Gnoth-404/Movement-Detection-using-24Ghz-Radar/hardware/10_SubCircuit_4thPassFilter/20_Simulation/sdhd_lab.asc

C1: cap; 100n
C2: polcap; 4.7µ
C3: cap; 1.5n
C4: polcap; 22µ
C5: polcap; 4.7µ
C6: cap; 3.3n
R1: res; 1k
R2: res; 1k
R3: res; 2.2k
R4: res; 33k
R5: res; 220k
R6: res; 100k
R7: res; 100
U1: UniversalOpAmp
U2: UniversalOpAmp
V1: voltage; 5
V2: voltage; ""; AC 1
Named nets: 0, out, in
.ac oct 10000 1 100000
* Gain Analysis Command
.meas gain_max MAX V(out)/V(in) FROM 1Hz TO 1Meg
 
* Corner Frequency Analysis Commands
.measure AC f_lower WHEN V(out)={Gain_max/sqrt(2)}
.measure f_upper when V(out)/V(in) = gain_max/sqrt(2) from 1MHz
 
* Low Pass Frequency Analysis Command
.measure f_low when V(out)/V(in) = gain_max/sqrt(2) from 1Hz
 
* High Pass Frequency Analysis Command
.measure f_high when V(out)/V(in) = gain_max/sqrt(2) from 1MHz
.lib opamp.sub
