Gnoth-404/Movement-Detection-using-24Ghz-Radar/software/firmware/Matlab_FFT.cydsn/bsw/led.c

/**
* \file <filename>
* \author <author-name>
* \date <date>
*
* \brief <Symbolic File name>
*
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
* \warning This software is a PROTOTYPE version and is not designed or intended for use in production, especially not for safety-critical applications!
* The user represents and warrants that it will NOT use or redistribute the Software for such purposes.
* This prototype is for research purposes only. This software is provided "AS IS," without a warranty of any kind.
*/

/*****************************************************************************/
/* Include files                                                             */
/*****************************************************************************/

#include "project.h"
#include "led.h"


/*****************************************************************************/
/* Local pre-processor symbols/macros ('#define')                            */
/*****************************************************************************/

/*****************************************************************************/
/* Global variable definitions (declared in header file with 'extern')       */
/*****************************************************************************/

/*****************************************************************************/
/* Local type definitions ('typedef')                                        */
/*****************************************************************************/



/*****************************************************************************/
/* Local variable definitions ('static')                                     */
/*****************************************************************************/


static LED_ONOFF_t LED__state[LED_ALL] = {LED_OFF, LED_OFF, LED_OFF}; /**< On/Off State of the LED, TRUE is on */

const static uint16 LED__Pulse_Width[256] = {
    0, 1, 1, 1, 1, 1, 1, 1, 1, 2, 2, 2, 2, 2, 2, 2, 2, 2, 2, 2, 2, 3,
    3, 3, 3, 3, 3, 3, 4, 4, 4, 4, 4, 4, 5, 5, 5, 5, 5, 6, 6, 6, 6, 7,
    7, 7, 8, 8, 8, 9, 9, 10, 10, 10, 11, 11, 12, 12, 13, 13, 14, 15,
    15, 16, 17, 17, 18, 19, 20, 21, 22, 23, 24, 25, 26, 27, 28, 29,
    31, 32, 33, 35, 36, 38, 40, 41, 43, 45, 47, 49, 52, 54, 56, 59,
    61, 64, 67, 70, 73, 76, 79, 83, 87, 91, 95, 99, 103, 108, 112,
    117, 123, 128, 134, 140, 146, 152, 159, 166, 173, 181, 189, 197,
    206, 215, 225, 235, 245, 256, 267, 279, 292, 304, 318, 332, 347,
    362, 378, 395, 412, 431, 450, 470, 490, 512, 535, 558, 583, 609,
    636, 664, 693, 724, 756, 790, 825, 861, 899, 939, 981, 1024, 1069,
    1117, 1166, 1218, 1272, 1328, 1387, 1448, 1512, 1579, 1649, 1722,
    1798, 1878, 1961, 2048, 2139, 2233, 2332, 2435, 2543, 2656, 2773,
    2896, 3025, 3158, 3298, 3444, 3597, 3756, 3922, 4096, 4277, 4467,
    4664, 4871, 5087, 5312, 5547, 5793, 6049, 6317, 6596, 6889, 7194,
    7512, 7845, 8192, 8555, 8933, 9329, 9742, 10173, 10624, 11094,
    11585, 12098, 12634, 13193, 13777, 14387, 15024, 15689, 16384,
    17109, 17867, 18658, 19484, 20346, 21247, 22188, 23170, 24196,
    25267, 26386, 27554, 28774, 30048, 31378, 32768, 34218, 35733,
    37315, 38967, 40693, 42494, 44376, 46340, 48392, 50534, 52772,
    55108, 57548, 60096, 62757, 65535
};

/*****************************************************************************/
/* Local function prototypes ('static')                                      */
/*****************************************************************************/

/**
 * Inverts the parameter
 * @param LED_ONOFF_t ledOnOff - Value to be inverted
 * @return inverted parameter
 */
static inline LED_ONOFF_t LED__toggleValue(LED_ONOFF_t ledOnOff);


/*****************************************************************************/
/* Function implementation - global ('extern') and local ('static')          */
/*****************************************************************************/

/**
 * Initialises the LED's and turns them off
 * @return RC_SUCCESS if function was executed as exepected, other error code in case of error
 */
RC_t LED_Init()
{
    RC_t result = RC_SUCCESS;
    
    for (LED_id_t i = LED_RED; i < LED_ALL; i++)
    {
        LED__state[i] = OFF;
        
        RC_t clearResult;
        clearResult = LED_Set(i, LED_OFF);
        
        if (clearResult != RC_SUCCESS)
        {
            //memorize error
            result = clearResult;
        }
    }

    return result;
}

/**
 * Sets the required LED
 * @param LED_t ledId - Identifier for the LED, ALL will change all LED's
 * @param LED_ONOFF_t ledOnOff - Trun the led on or off
 * @return RC_SUCCESS if function was executed as exepected, other error code in case of error
 */
RC_t LED_Set(LED_id_t ledId, LED_ONOFF_t ledOnOff)
{
    //set individual LED
    switch (ledId)
    {
        case LED_RED : 
            LED_red_Write(ledOnOff); 
            LED__state[ledId] = ledOnOff; 
            break;
        
        case LED_YELLOW : 
            LED_yellow_Write(ledOnOff); 
            LED__state[ledId] = ledOnOff;
            break;
            
        case LED_GREEN : 
            LED_green_Write(ledOnOff); 
            LED__state[ledId] = ledOnOff;
            break;
           
        case LED_ALL : 
            for (LED_id_t i = LED_RED; i < LED_ALL; i++)
            {
                LED_Set(i, ledOnOff);
            }
            break;
        default: return RC_ERROR_BAD_PARAM;
    }
    
    return RC_SUCCESS;
}



/**
 * Toggle the required LED
 * @param LED_t ledId - Identifier for the LED, ALL will change all LED's
 * @return RC_SUCCESS if function was executed as exepected, other error code in case of error
 */
RC_t LED_Toggle(LED_id_t ledId)
{
    //set individual LED
    switch (ledId)
    {
        case LED_RED : 
            LED__state[ledId] = LED__toggleValue(LED__state[ledId]); 
            LED_red_Write(LED__state[ledId]);
            break;
        
        case LED_YELLOW : 
            LED__state[ledId] = LED__toggleValue(LED__state[ledId]); 
            LED_yellow_Write(LED__state[ledId]);
            break;
            
        case LED_GREEN : 
            LED__state[ledId] = LED__toggleValue(LED__state[ledId]); 
            LED_green_Write(LED__state[ledId]);
            break;
           
        case LED_ALL : 
            for (LED_id_t i = LED_RED; i < LED_ALL; i++)
            {
                LED_Toggle(i);
            }
            break;
        default: return RC_ERROR_BAD_PARAM;
    }
    
    return RC_SUCCESS;
}


/**
 * Inverts the parameter
 * @param LED_ONOFF_t ledOnOff - Value to be inverted
 * @return inverted parameter
 */
static inline LED_ONOFF_t LED__toggleValue(LED_ONOFF_t ledOnOff)
{
    if (ledOnOff == LED_ON) 
    {
        return LED_OFF;
    }
    else
    {
        return LED_ON;
    }
}
