Gnoth-404/Movement-Detection-using-24Ghz-Radar/software/firmware/Matlab_FFT.cydsn/codegentemp/Button.h

/*******************************************************************************
* File Name: Button.h  
* Version 2.20
*
* Description:
*  This file contains Pin function prototypes and register defines
*
* Note:
*
********************************************************************************
* Copyright 2008-2015, Cypress Semiconductor Corporation.  All rights reserved.
* You may use this file only in accordance with the license, terms, conditions, 
* disclaimers, and limitations in the end user license agreement accompanying 
* the software package with which this file was provided.
*******************************************************************************/

#if !defined(CY_PINS_Button_H) /* Pins Button_H */
#define CY_PINS_Button_H

#include "cytypes.h"
#include "cyfitter.h"
#include "cypins.h"
#include "Button_aliases.h"

/* APIs are not generated for P15[7:6] */
#if !(CY_PSOC5A &&\
	 Button__PORT == 15 && ((Button__MASK & 0xC0) != 0))


/***************************************
*        Function Prototypes             
***************************************/    

/**
* \addtogroup group_general
* @{
*/
void    Button_Write(uint8 value);
void    Button_SetDriveMode(uint8 mode);
uint8   Button_ReadDataReg(void);
uint8   Button_Read(void);
void    Button_SetInterruptMode(uint16 position, uint16 mode);
uint8   Button_ClearInterrupt(void);
/** @} general */

/***************************************
*           API Constants        
***************************************/
/**
* \addtogroup group_constants
* @{
*/
    /** \addtogroup driveMode Drive mode constants
     * \brief Constants to be passed as "mode" parameter in the Button_SetDriveMode() function.
     *  @{
     */
        #define Button_DM_ALG_HIZ         PIN_DM_ALG_HIZ
        #define Button_DM_DIG_HIZ         PIN_DM_DIG_HIZ
        #define Button_DM_RES_UP          PIN_DM_RES_UP
        #define Button_DM_RES_DWN         PIN_DM_RES_DWN
        #define Button_DM_OD_LO           PIN_DM_OD_LO
        #define Button_DM_OD_HI           PIN_DM_OD_HI
        #define Button_DM_STRONG          PIN_DM_STRONG
        #define Button_DM_RES_UPDWN       PIN_DM_RES_UPDWN
    /** @} driveMode */
/** @} group_constants */
    
/* Digital Port Constants */
#define Button_MASK               Button__MASK
#define Button_SHIFT              Button__SHIFT
#define Button_WIDTH              1u

/* Interrupt constants */
#if defined(Button__INTSTAT)
/**
* \addtogroup group_constants
* @{
*/
    /** \addtogroup intrMode Interrupt constants
     * \brief Constants to be passed as "mode" parameter in Button_SetInterruptMode() function.
     *  @{
     */
        #define Button_INTR_NONE      (uint16)(0x0000u)
        #define Button_INTR_RISING    (uint16)(0x0001u)
        #define Button_INTR_FALLING   (uint16)(0x0002u)
        #define Button_INTR_BOTH      (uint16)(0x0003u) 
    /** @} intrMode */
/** @} group_constants */

    #define Button_INTR_MASK      (0x01u) 
#endif /* (Button__INTSTAT) */


/***************************************
*             Registers        
***************************************/

/* Main Port Registers */
/* Pin State */
#define Button_PS                     (* (reg8 *) Button__PS)
/* Data Register */
#define Button_DR                     (* (reg8 *) Button__DR)
/* Port Number */
#define Button_PRT_NUM                (* (reg8 *) Button__PRT) 
/* Connect to Analog Globals */                                                  
#define Button_AG                     (* (reg8 *) Button__AG)                       
/* Analog MUX bux enable */
#define Button_AMUX                   (* (reg8 *) Button__AMUX) 
/* Bidirectional Enable */                                                        
#define Button_BIE                    (* (reg8 *) Button__BIE)
/* Bit-mask for Aliased Register Access */
#define Button_BIT_MASK               (* (reg8 *) Button__BIT_MASK)
/* Bypass Enable */
#define Button_BYP                    (* (reg8 *) Button__BYP)
/* Port wide control signals */                                                   
#define Button_CTL                    (* (reg8 *) Button__CTL)
/* Drive Modes */
#define Button_DM0                    (* (reg8 *) Button__DM0) 
#define Button_DM1                    (* (reg8 *) Button__DM1)
#define Button_DM2                    (* (reg8 *) Button__DM2) 
/* Input Buffer Disable Override */
#define Button_INP_DIS                (* (reg8 *) Button__INP_DIS)
/* LCD Common or Segment Drive */
#define Button_LCD_COM_SEG            (* (reg8 *) Button__LCD_COM_SEG)
/* Enable Segment LCD */
#define Button_LCD_EN                 (* (reg8 *) Button__LCD_EN)
/* Slew Rate Control */
#define Button_SLW                    (* (reg8 *) Button__SLW)

/* DSI Port Registers */
/* Global DSI Select Register */
#define Button_PRTDSI__CAPS_SEL       (* (reg8 *) Button__PRTDSI__CAPS_SEL) 
/* Double Sync Enable */
#define Button_PRTDSI__DBL_SYNC_IN    (* (reg8 *) Button__PRTDSI__DBL_SYNC_IN) 
/* Output Enable Select Drive Strength */
#define Button_PRTDSI__OE_SEL0        (* (reg8 *) Button__PRTDSI__OE_SEL0) 
#define Button_PRTDSI__OE_SEL1        (* (reg8 *) Button__PRTDSI__OE_SEL1) 
/* Port Pin Output Select Registers */
#define Button_PRTDSI__OUT_SEL0       (* (reg8 *) Button__PRTDSI__OUT_SEL0) 
#define Button_PRTDSI__OUT_SEL1       (* (reg8 *) Button__PRTDSI__OUT_SEL1) 
/* Sync Output Enable Registers */
#define Button_PRTDSI__SYNC_OUT       (* (reg8 *) Button__PRTDSI__SYNC_OUT) 

/* SIO registers */
#if defined(Button__SIO_CFG)
    #define Button_SIO_HYST_EN        (* (reg8 *) Button__SIO_HYST_EN)
    #define Button_SIO_REG_HIFREQ     (* (reg8 *) Button__SIO_REG_HIFREQ)
    #define Button_SIO_CFG            (* (reg8 *) Button__SIO_CFG)
    #define Button_SIO_DIFF           (* (reg8 *) Button__SIO_DIFF)
#endif /* (Button__SIO_CFG) */

/* Interrupt Registers */
#if defined(Button__INTSTAT)
    #define Button_INTSTAT            (* (reg8 *) Button__INTSTAT)
    #define Button_SNAP               (* (reg8 *) Button__SNAP)
    
	#define Button_0_INTTYPE_REG 		(* (reg8 *) Button__0__INTTYPE)
#endif /* (Button__INTSTAT) */

#endif /* CY_PSOC5A... */

#endif /*  CY_PINS_Button_H */


/* [] END OF FILE */
