Gnoth-404/Movement-Detection-using-24Ghz-Radar/software/firmware/Matlab_FFT.cydsn/codegentemp/Status_Reg_1.c

/*******************************************************************************
* File Name: Status_Reg_1.c  
* Version 1.90
*
* Description:
*  This file contains API to enable firmware to read the value of a Status 
*  Register.
*
* Note:
*
********************************************************************************
* Copyright 2008-2015, Cypress Semiconductor Corporation.  All rights reserved.
* You may use this file only in accordance with the license, terms, conditions, 
* disclaimers, and limitations in the end user license agreement accompanying 
* the software package with which this file was provided.
*******************************************************************************/

#include "Status_Reg_1.h"

#if !defined(Status_Reg_1_sts_sts_reg__REMOVED) /* Check for removal by optimization */


/*******************************************************************************
* Function Name: Status_Reg_1_Read
********************************************************************************
*
* Summary:
*  Reads the current value assigned to the Status Register.
*
* Parameters:
*  None.
*
* Return:
*  The current value in the Status Register.
*
*******************************************************************************/
uint8 Status_Reg_1_Read(void) 
{ 
    return Status_Reg_1_Status;
}


/*******************************************************************************
* Function Name: Status_Reg_1_InterruptEnable
********************************************************************************
*
* Summary:
*  Enables the Status Register interrupt.
*
* Parameters:
*  None.
*
* Return:
*  None.
*
*******************************************************************************/
void Status_Reg_1_InterruptEnable(void) 
{
    uint8 interruptState;
    interruptState = CyEnterCriticalSection();
    Status_Reg_1_Status_Aux_Ctrl |= Status_Reg_1_STATUS_INTR_ENBL;
    CyExitCriticalSection(interruptState);
}


/*******************************************************************************
* Function Name: Status_Reg_1_InterruptDisable
********************************************************************************
*
* Summary:
*  Disables the Status Register interrupt.
*
* Parameters:
*  None.
*
* Return:
*  None.
*
*******************************************************************************/
void Status_Reg_1_InterruptDisable(void) 
{
    uint8 interruptState;
    interruptState = CyEnterCriticalSection();
    Status_Reg_1_Status_Aux_Ctrl &= (uint8)(~Status_Reg_1_STATUS_INTR_ENBL);
    CyExitCriticalSection(interruptState);
}


/*******************************************************************************
* Function Name: Status_Reg_1_WriteMask
********************************************************************************
*
* Summary:
*  Writes the current mask value assigned to the Status Register.
*
* Parameters:
*  mask:  Value to write into the mask register.
*
* Return:
*  None.
*
*******************************************************************************/
void Status_Reg_1_WriteMask(uint8 mask) 
{
    #if(Status_Reg_1_INPUTS < 8u)
    	mask &= ((uint8)(1u << Status_Reg_1_INPUTS) - 1u);
	#endif /* End Status_Reg_1_INPUTS < 8u */
    Status_Reg_1_Status_Mask = mask;
}


/*******************************************************************************
* Function Name: Status_Reg_1_ReadMask
********************************************************************************
*
* Summary:
*  Reads the current interrupt mask assigned to the Status Register.
*
* Parameters:
*  None.
*
* Return:
*  The value of the interrupt mask of the Status Register.
*
*******************************************************************************/
uint8 Status_Reg_1_ReadMask(void) 
{
    return Status_Reg_1_Status_Mask;
}

#endif /* End check for removal by optimization */


/* [] END OF FILE */
