Gnoth-404/Movement-Detection-using-24Ghz-Radar/software/firmware/Matlab_FFT.cydsn/codegentemp/UART_LOG_PM.c

/*******************************************************************************
* File Name: UART_LOG_PM.c
* Version 2.50
*
* Description:
*  This file provides Sleep/WakeUp APIs functionality.
*
* Note:
*
********************************************************************************
* Copyright 2008-2015, Cypress Semiconductor Corporation.  All rights reserved.
* You may use this file only in accordance with the license, terms, conditions,
* disclaimers, and limitations in the end user license agreement accompanying
* the software package with which this file was provided.
*******************************************************************************/

#include "UART_LOG.h"


/***************************************
* Local data allocation
***************************************/

static UART_LOG_BACKUP_STRUCT  UART_LOG_backup =
{
    /* enableState - disabled */
    0u,
};



/*******************************************************************************
* Function Name: UART_LOG_SaveConfig
********************************************************************************
*
* Summary:
*  This function saves the component nonretention control register.
*  Does not save the FIFO which is a set of nonretention registers.
*  This function is called by the UART_LOG_Sleep() function.
*
* Parameters:
*  None.
*
* Return:
*  None.
*
* Global Variables:
*  UART_LOG_backup - modified when non-retention registers are saved.
*
* Reentrant:
*  No.
*
*******************************************************************************/
void UART_LOG_SaveConfig(void)
{
    #if(UART_LOG_CONTROL_REG_REMOVED == 0u)
        UART_LOG_backup.cr = UART_LOG_CONTROL_REG;
    #endif /* End UART_LOG_CONTROL_REG_REMOVED */
}


/*******************************************************************************
* Function Name: UART_LOG_RestoreConfig
********************************************************************************
*
* Summary:
*  Restores the nonretention control register except FIFO.
*  Does not restore the FIFO which is a set of nonretention registers.
*
* Parameters:
*  None.
*
* Return:
*  None.
*
* Global Variables:
*  UART_LOG_backup - used when non-retention registers are restored.
*
* Reentrant:
*  No.
*
* Notes:
*  If this function is called without calling UART_LOG_SaveConfig() 
*  first, the data loaded may be incorrect.
*
*******************************************************************************/
void UART_LOG_RestoreConfig(void)
{
    #if(UART_LOG_CONTROL_REG_REMOVED == 0u)
        UART_LOG_CONTROL_REG = UART_LOG_backup.cr;
    #endif /* End UART_LOG_CONTROL_REG_REMOVED */
}


/*******************************************************************************
* Function Name: UART_LOG_Sleep
********************************************************************************
*
* Summary:
*  This is the preferred API to prepare the component for sleep. 
*  The UART_LOG_Sleep() API saves the current component state. Then it
*  calls the UART_LOG_Stop() function and calls 
*  UART_LOG_SaveConfig() to save the hardware configuration.
*  Call the UART_LOG_Sleep() function before calling the CyPmSleep() 
*  or the CyPmHibernate() function. 
*
* Parameters:
*  None.
*
* Return:
*  None.
*
* Global Variables:
*  UART_LOG_backup - modified when non-retention registers are saved.
*
* Reentrant:
*  No.
*
*******************************************************************************/
void UART_LOG_Sleep(void)
{
    #if(UART_LOG_RX_ENABLED || UART_LOG_HD_ENABLED)
        if((UART_LOG_RXSTATUS_ACTL_REG  & UART_LOG_INT_ENABLE) != 0u)
        {
            UART_LOG_backup.enableState = 1u;
        }
        else
        {
            UART_LOG_backup.enableState = 0u;
        }
    #else
        if((UART_LOG_TXSTATUS_ACTL_REG  & UART_LOG_INT_ENABLE) !=0u)
        {
            UART_LOG_backup.enableState = 1u;
        }
        else
        {
            UART_LOG_backup.enableState = 0u;
        }
    #endif /* End UART_LOG_RX_ENABLED || UART_LOG_HD_ENABLED*/

    UART_LOG_Stop();
    UART_LOG_SaveConfig();
}


/*******************************************************************************
* Function Name: UART_LOG_Wakeup
********************************************************************************
*
* Summary:
*  This is the preferred API to restore the component to the state when 
*  UART_LOG_Sleep() was called. The UART_LOG_Wakeup() function
*  calls the UART_LOG_RestoreConfig() function to restore the 
*  configuration. If the component was enabled before the 
*  UART_LOG_Sleep() function was called, the UART_LOG_Wakeup()
*  function will also re-enable the component.
*
* Parameters:
*  None.
*
* Return:
*  None.
*
* Global Variables:
*  UART_LOG_backup - used when non-retention registers are restored.
*
* Reentrant:
*  No.
*
*******************************************************************************/
void UART_LOG_Wakeup(void)
{
    UART_LOG_RestoreConfig();
    #if( (UART_LOG_RX_ENABLED) || (UART_LOG_HD_ENABLED) )
        UART_LOG_ClearRxBuffer();
    #endif /* End (UART_LOG_RX_ENABLED) || (UART_LOG_HD_ENABLED) */
    #if(UART_LOG_TX_ENABLED || UART_LOG_HD_ENABLED)
        UART_LOG_ClearTxBuffer();
    #endif /* End UART_LOG_TX_ENABLED || UART_LOG_HD_ENABLED */

    if(UART_LOG_backup.enableState != 0u)
    {
        UART_LOG_Enable();
    }
}


/* [] END OF FILE */
