Gnoth-404/Movement-Detection-using-24Ghz-Radar/software/firmware/Matlab_FFT.cydsn/codegentemp/WaveDAC8_BuffAmp.c

/*******************************************************************************
* File Name: WaveDAC8_BuffAmp.c
* Version 1.90
*
* Description:
*  This file provides the source code to the API for OpAmp (Analog Buffer) 
*  Component.
*
* Note:
*
********************************************************************************
* Copyright 2008-2012, Cypress Semiconductor Corporation.  All rights reserved.
* You may use this file only in accordance with the license, terms, conditions, 
* disclaimers, and limitations in the end user license agreement accompanying 
* the software package with which this file was provided.
*******************************************************************************/

#include "WaveDAC8_BuffAmp.h"

uint8 WaveDAC8_BuffAmp_initVar = 0u;


/*******************************************************************************   
* Function Name: WaveDAC8_BuffAmp_Init
********************************************************************************
*
* Summary:
*  Initialize component's parameters to the parameters set by user in the 
*  customizer of the component placed onto schematic. Usually called in 
*  WaveDAC8_BuffAmp_Start().
*
* Parameters:
*  void
*
* Return:
*  void
*
*******************************************************************************/
void WaveDAC8_BuffAmp_Init(void) 
{
    WaveDAC8_BuffAmp_SetPower(WaveDAC8_BuffAmp_DEFAULT_POWER);
}


/*******************************************************************************   
* Function Name: WaveDAC8_BuffAmp_Enable
********************************************************************************
*
* Summary:
*  Enables the OpAmp block operation
*
* Parameters:
*  void
*
* Return:
*  void
*
*******************************************************************************/
void WaveDAC8_BuffAmp_Enable(void) 
{
    /* Enable negative charge pumps in ANIF */
    WaveDAC8_BuffAmp_PUMP_CR1_REG  |= (WaveDAC8_BuffAmp_PUMP_CR1_CLKSEL | WaveDAC8_BuffAmp_PUMP_CR1_FORCE);

    /* Enable power to buffer in active mode */
    WaveDAC8_BuffAmp_PM_ACT_CFG_REG |= WaveDAC8_BuffAmp_ACT_PWR_EN;

    /* Enable power to buffer in alternative active mode */
    WaveDAC8_BuffAmp_PM_STBY_CFG_REG |= WaveDAC8_BuffAmp_STBY_PWR_EN;
}


/*******************************************************************************
* Function Name:   WaveDAC8_BuffAmp_Start
********************************************************************************
*
* Summary:
*  The start function initializes the Analog Buffer with the default values and 
*  sets the power to the given level. A power level of 0, is same as 
*  executing the stop function.
*
* Parameters:
*  void
*
* Return:
*  void
*
* Global variables:
*  WaveDAC8_BuffAmp_initVar: Used to check the initial configuration, modified 
*  when this function is called for the first time.
*
*******************************************************************************/
void WaveDAC8_BuffAmp_Start(void) 
{
    if(WaveDAC8_BuffAmp_initVar == 0u)
    {
        WaveDAC8_BuffAmp_initVar = 1u;
        WaveDAC8_BuffAmp_Init();
    }

    WaveDAC8_BuffAmp_Enable();
}


/*******************************************************************************
* Function Name: WaveDAC8_BuffAmp_Stop
********************************************************************************
*
* Summary:
*  Powers down amplifier to lowest power state.
*
* Parameters:
*  void
*
* Return:
*  void
*
*******************************************************************************/
void WaveDAC8_BuffAmp_Stop(void) 
{
    /* Disable power to buffer in active mode template */
    WaveDAC8_BuffAmp_PM_ACT_CFG_REG &= (uint8)(~WaveDAC8_BuffAmp_ACT_PWR_EN);

    /* Disable power to buffer in alternative active mode template */
    WaveDAC8_BuffAmp_PM_STBY_CFG_REG &= (uint8)(~WaveDAC8_BuffAmp_STBY_PWR_EN);
    
    /* Disable negative charge pumps for ANIF only if all ABuf is turned OFF */
    if(WaveDAC8_BuffAmp_PM_ACT_CFG_REG == 0u)
    {
        WaveDAC8_BuffAmp_PUMP_CR1_REG &= (uint8)(~(WaveDAC8_BuffAmp_PUMP_CR1_CLKSEL | WaveDAC8_BuffAmp_PUMP_CR1_FORCE));
    }
}


/*******************************************************************************
* Function Name: WaveDAC8_BuffAmp_SetPower
********************************************************************************
*
* Summary:
*  Sets power level of Analog buffer.
*
* Parameters: 
*  power: PSoC3: Sets power level between low (1) and high power (3).
*         PSoC5: Sets power level High (0)
*
* Return:
*  void
*
**********************************************************************************/
void WaveDAC8_BuffAmp_SetPower(uint8 power) 
{
    #if (CY_PSOC3 || CY_PSOC5LP)
        WaveDAC8_BuffAmp_CR_REG &= (uint8)(~WaveDAC8_BuffAmp_PWR_MASK);
        WaveDAC8_BuffAmp_CR_REG |= power & WaveDAC8_BuffAmp_PWR_MASK;      /* Set device power */
    #else
        CYASSERT(WaveDAC8_BuffAmp_HIGHPOWER == power);
    #endif /* CY_PSOC3 || CY_PSOC5LP */
}


/* [] END OF FILE */
