Gnoth-404/Movement-Detection-using-24Ghz-Radar/software/firmware/Matlab_FFT.cydsn/codegentemp/WaveDAC8_VDAC8_PM.c

/*******************************************************************************
* File Name: WaveDAC8_VDAC8_PM.c  
* Version 1.90
*
* Description:
*  This file provides the power management source code to API for the
*  VDAC8.  
*
* Note:
*  None
*
********************************************************************************
* Copyright 2008-2012, Cypress Semiconductor Corporation.  All rights reserved.
* You may use this file only in accordance with the license, terms, conditions, 
* disclaimers, and limitations in the end user license agreement accompanying 
* the software package with which this file was provided.
*******************************************************************************/

#include "WaveDAC8_VDAC8.h"

static WaveDAC8_VDAC8_backupStruct WaveDAC8_VDAC8_backup;


/*******************************************************************************
* Function Name: WaveDAC8_VDAC8_SaveConfig
********************************************************************************
* Summary:
*  Save the current user configuration
*
* Parameters:  
*  void  
*
* Return: 
*  void
*
*******************************************************************************/
void WaveDAC8_VDAC8_SaveConfig(void) 
{
    if (!((WaveDAC8_VDAC8_CR1 & WaveDAC8_VDAC8_SRC_MASK) == WaveDAC8_VDAC8_SRC_UDB))
    {
        WaveDAC8_VDAC8_backup.data_value = WaveDAC8_VDAC8_Data;
    }
}


/*******************************************************************************
* Function Name: WaveDAC8_VDAC8_RestoreConfig
********************************************************************************
*
* Summary:
*  Restores the current user configuration.
*
* Parameters:  
*  void
*
* Return: 
*  void
*
*******************************************************************************/
void WaveDAC8_VDAC8_RestoreConfig(void) 
{
    if (!((WaveDAC8_VDAC8_CR1 & WaveDAC8_VDAC8_SRC_MASK) == WaveDAC8_VDAC8_SRC_UDB))
    {
        if((WaveDAC8_VDAC8_Strobe & WaveDAC8_VDAC8_STRB_MASK) == WaveDAC8_VDAC8_STRB_EN)
        {
            WaveDAC8_VDAC8_Strobe &= (uint8)(~WaveDAC8_VDAC8_STRB_MASK);
            WaveDAC8_VDAC8_Data = WaveDAC8_VDAC8_backup.data_value;
            WaveDAC8_VDAC8_Strobe |= WaveDAC8_VDAC8_STRB_EN;
        }
        else
        {
            WaveDAC8_VDAC8_Data = WaveDAC8_VDAC8_backup.data_value;
        }
    }
}


/*******************************************************************************
* Function Name: WaveDAC8_VDAC8_Sleep
********************************************************************************
* Summary:
*  Stop and Save the user configuration
*
* Parameters:  
*  void:  
*
* Return: 
*  void
*
* Global variables:
*  WaveDAC8_VDAC8_backup.enableState:  Is modified depending on the enable 
*  state  of the block before entering sleep mode.
*
*******************************************************************************/
void WaveDAC8_VDAC8_Sleep(void) 
{
    /* Save VDAC8's enable state */    
    if(WaveDAC8_VDAC8_ACT_PWR_EN == (WaveDAC8_VDAC8_PWRMGR & WaveDAC8_VDAC8_ACT_PWR_EN))
    {
        /* VDAC8 is enabled */
        WaveDAC8_VDAC8_backup.enableState = 1u;
    }
    else
    {
        /* VDAC8 is disabled */
        WaveDAC8_VDAC8_backup.enableState = 0u;
    }
    
    WaveDAC8_VDAC8_Stop();
    WaveDAC8_VDAC8_SaveConfig();
}


/*******************************************************************************
* Function Name: WaveDAC8_VDAC8_Wakeup
********************************************************************************
*
* Summary:
*  Restores and enables the user configuration
*  
* Parameters:  
*  void
*
* Return: 
*  void
*
* Global variables:
*  WaveDAC8_VDAC8_backup.enableState:  Is used to restore the enable state of 
*  block on wakeup from sleep mode.
*
*******************************************************************************/
void WaveDAC8_VDAC8_Wakeup(void) 
{
    WaveDAC8_VDAC8_RestoreConfig();
    
    if(WaveDAC8_VDAC8_backup.enableState == 1u)
    {
        /* Enable VDAC8's operation */
        WaveDAC8_VDAC8_Enable();

        /* Restore the data register */
        WaveDAC8_VDAC8_SetValue(WaveDAC8_VDAC8_Data);
    } /* Do nothing if VDAC8 was disabled before */    
}


/* [] END OF FILE */
