Gnoth-404/Movement-Detection-using-24Ghz-Radar/software/firmware/Matlab_FFT.cydsn/codegentemp/isr_rx.h

/*******************************************************************************
* File Name: isr_rx.h
* Version 1.71
*
*  Description:
*   Provides the function definitions for the Interrupt Controller.
*
*
********************************************************************************
* Copyright 2008-2015, Cypress Semiconductor Corporation.  All rights reserved.
* You may use this file only in accordance with the license, terms, conditions, 
* disclaimers, and limitations in the end user license agreement accompanying 
* the software package with which this file was provided.
*******************************************************************************/
#if !defined(CY_ISR_isr_rx_H)
#define CY_ISR_isr_rx_H


#include <cytypes.h>
#include <cyfitter.h>

/* Interrupt Controller API. */
void isr_rx_Start(void);
void isr_rx_StartEx(cyisraddress address);
void isr_rx_Stop(void);

CY_ISR_PROTO(isr_rx_Interrupt);

void isr_rx_SetVector(cyisraddress address);
cyisraddress isr_rx_GetVector(void);

void isr_rx_SetPriority(uint8 priority);
uint8 isr_rx_GetPriority(void);

void isr_rx_Enable(void);
uint8 isr_rx_GetState(void);
void isr_rx_Disable(void);

void isr_rx_SetPending(void);
void isr_rx_ClearPending(void);


/* Interrupt Controller Constants */

/* Address of the INTC.VECT[x] register that contains the Address of the isr_rx ISR. */
#define isr_rx_INTC_VECTOR            ((reg32 *) isr_rx__INTC_VECT)

/* Address of the isr_rx ISR priority. */
#define isr_rx_INTC_PRIOR             ((reg8 *) isr_rx__INTC_PRIOR_REG)

/* Priority of the isr_rx interrupt. */
#define isr_rx_INTC_PRIOR_NUMBER      isr_rx__INTC_PRIOR_NUM

/* Address of the INTC.SET_EN[x] byte to bit enable isr_rx interrupt. */
#define isr_rx_INTC_SET_EN            ((reg32 *) isr_rx__INTC_SET_EN_REG)

/* Address of the INTC.CLR_EN[x] register to bit clear the isr_rx interrupt. */
#define isr_rx_INTC_CLR_EN            ((reg32 *) isr_rx__INTC_CLR_EN_REG)

/* Address of the INTC.SET_PD[x] register to set the isr_rx interrupt state to pending. */
#define isr_rx_INTC_SET_PD            ((reg32 *) isr_rx__INTC_SET_PD_REG)

/* Address of the INTC.CLR_PD[x] register to clear the isr_rx interrupt. */
#define isr_rx_INTC_CLR_PD            ((reg32 *) isr_rx__INTC_CLR_PD_REG)


#endif /* CY_ISR_isr_rx_H */


/* [] END OF FILE */
